SphericalCowww/CubicDoggo_06R/src/my_robot_description/mesh/CADv2/thighInner.FCStd

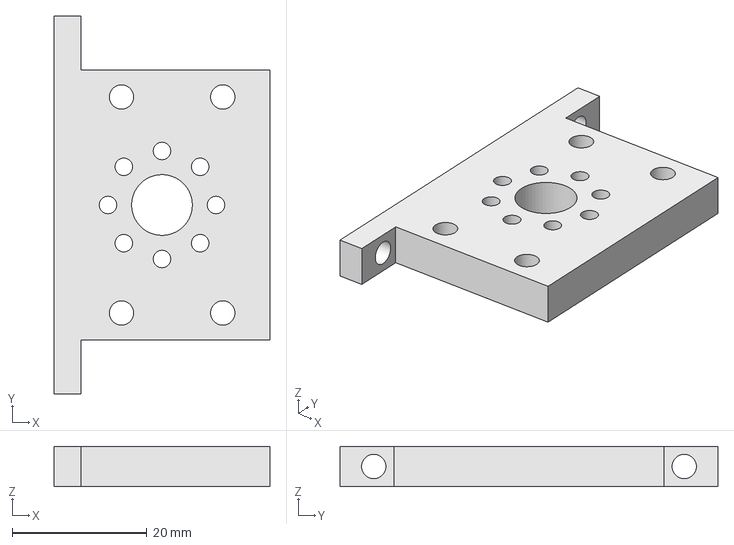
[picture p27: CAD file, 2026-06-20]
src/my_robot_description/mesh/CADv2/thighInner.FCStd
32.0 x 56.0 x 6.00 mm
