SphericalCowww/CubicDoggo_06R/src/my_robot_description/mesh/CADv2/XL430rotorPadding.FCStd

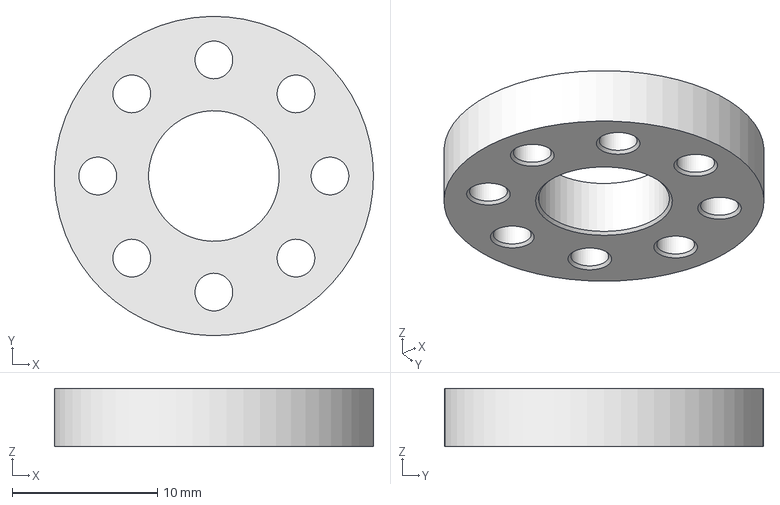
[picture p28: CAD file, 2026-06-20]
src/my_robot_description/mesh/CADv2/XL430rotorPadding.FCStd
22.0 x 22.0 x 4.00 mm
