SphericalCowww/CubicDoggo_06R/src/my_robot_description/mesh/CADv2/calfJoint.FCStd

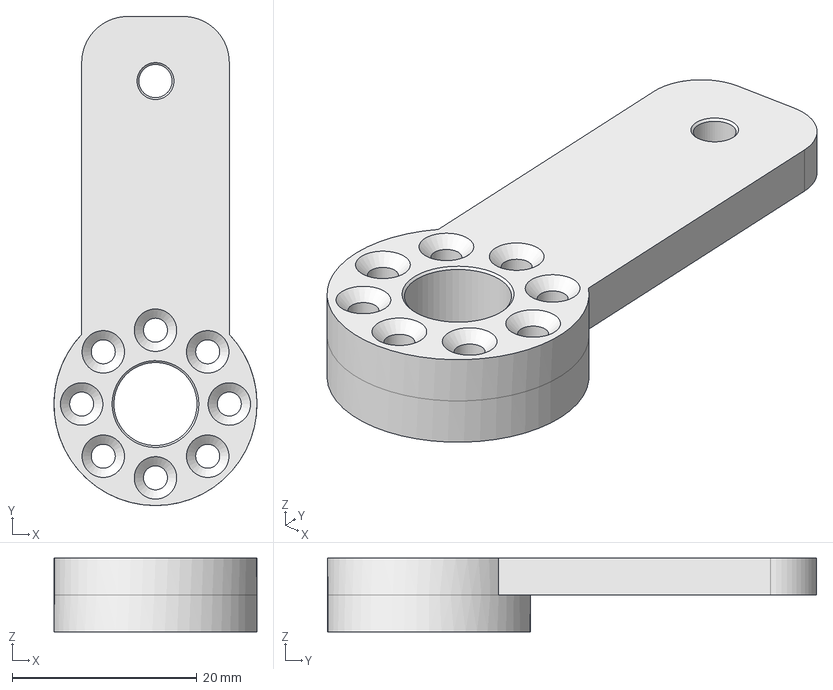
[picture p29: CAD file, 2026-06-20]
src/my_robot_description/mesh/CADv2/calfJoint.FCStd
22.0 x 53.0 x 8.00 mm
