SphericalCowww/CubicDoggo_06R/src/my_robot_description/mesh/CADv2/thighOuter.FCStd

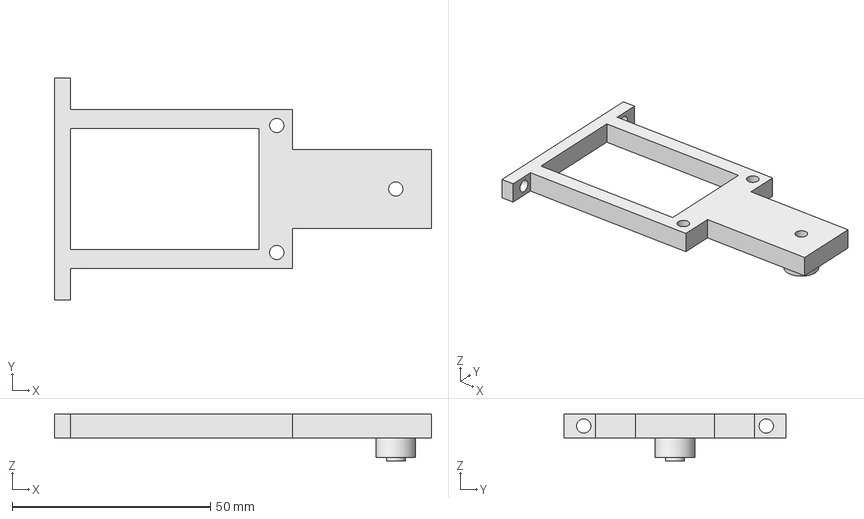
[picture p30: CAD file, 2026-06-20]
src/my_robot_description/mesh/CADv2/thighOuter.FCStd
95.0 x 56.0 x 11.8 mm
