SphericalCowww/CubicDoggo_06R/src/my_robot_description/mesh/CADv2/XL430holderBasic.FCStd

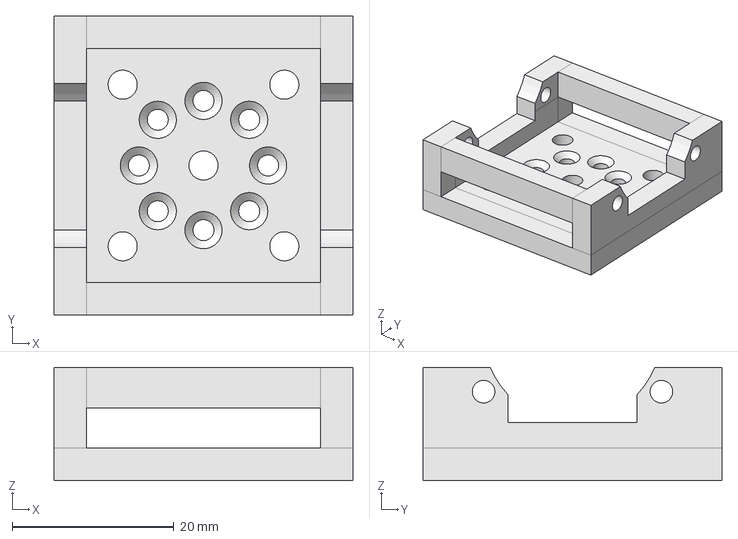
[picture p31: CAD file, 2026-06-20]
src/my_robot_description/mesh/CADv2/XL430holderBasic.FCStd
37.0 x 37.0 x 14.0 mm
