SphericalCowww/CubicDoggo_06R/src/my_robot_description/mesh/CADv2/bodyHolderWide.FCStd

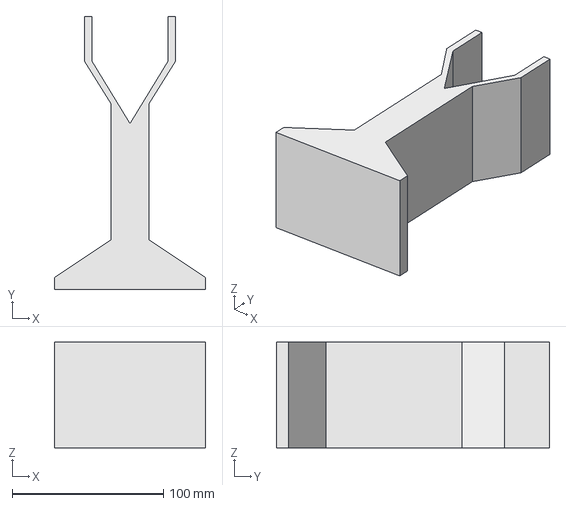
[picture p32: CAD file, 2026-06-20]
src/my_robot_description/mesh/CADv2/bodyHolderWide.FCStd
100.0 x 181.0 x 70.0 mm
